maxritter/diy-thermocam/firmware/3.0/src/general/colorschemes.cpp

/*
 *
 * COLOR SCHEMES - Contains 19 different color schemes to display the thermal image
 *
 * DIY-Thermocam Firmware
 *
 * GNU General Public License v3.0
 *
 * Copyright by Max Ritter
 *
 * http://www.diy-thermocam.net
 * https://github.com/maxritter/diy-thermocam
 *
 */

/*################################# INCLUDES ##################################*/

#include <Arduino.h>
#include <colorschemes.h>

/*############################# PUBLIC VARIABLES ##############################*/

const byte colorMap_arctic[] = { 15, 16, 146, 15, 16, 146, 15, 15, 153, 15, 15, 153, 15, 15, 159, 15, 15, 159, 16, 15, 167, 16, 15, 167, 15, 15, 175, 15, 15, 175, 16, 15, 182, 16, 15, 182, 16, 16, 190, 16, 16, 190, 14, 15, 197, 14, 15, 197, 15, 15, 205, 15, 15, 205, 15, 15, 211, 15, 15, 211, 16, 15, 219, 16, 15, 219, 16, 15, 227, 16, 15, 227, 16, 18, 239, 16, 18, 239, 16, 25, 240, 16, 25, 240, 15, 34, 239, 15, 34, 239, 15, 44, 238, 15, 44, 238, 14, 54, 239, 14, 54, 239, 14, 63, 239, 14, 63, 239, 14, 74, 238, 14, 74, 238, 17, 82, 238, 17, 82, 238, 19, 92, 237, 19, 92, 237, 22, 102, 239, 22, 102, 239, 24, 111, 238, 24, 111, 238, 27, 120, 237, 27, 120, 237, 28, 131, 237, 28, 131, 237, 32, 140, 237, 32, 140, 237, 34, 150, 237, 34, 150, 237, 36, 160, 236, 36, 160, 236, 39, 168, 237, 39, 168, 237, 42, 179, 237, 42, 179, 237, 44, 188, 236, 44, 188, 236, 46, 197, 236, 46, 197, 236, 49, 208, 236, 49, 208, 236, 52, 217, 235, 52, 217, 235, 54, 227, 232, 54, 227, 232, 57, 227, 230, 57, 227, 230, 58, 226, 227, 58, 226, 227, 62, 224, 225, 62, 224, 225, 64, 222, 222, 64, 222, 222, 66, 220, 220, 66, 220, 220, 67, 215, 215, 67, 215, 215, 69, 209, 210, 69, 209, 210, 73, 205, 204, 73, 205, 204, 76, 198, 199, 76, 198, 199, 79, 193, 192, 79, 193, 192, 81, 187, 187, 81, 187, 187, 83, 181, 180, 83, 181, 180, 87, 175, 175, 87, 175, 175, 88, 170, 170, 88, 170, 170, 88, 164, 165, 88, 164, 165, 90, 158, 159, 90, 158, 159, 90, 152, 153, 90, 152, 153, 90, 146, 145, 90, 146, 145, 92, 140, 140, 92, 140, 140, 92, 134, 134, 92, 134, 134, 95, 129, 129, 95, 129, 129, 95, 123, 123, 95, 123, 123, 96, 117, 116, 96, 117, 116, 97, 111, 110, 97, 111, 110, 99, 105, 105, 99, 105, 105, 102, 102, 102, 102, 102, 102, 107, 101, 97, 107, 101, 97, 112, 101, 95, 112, 101, 95, 117, 101, 90, 117, 101, 90, 123, 102, 87, 123, 102, 87, 129, 101, 84, 129, 101, 84, 134, 101, 80, 134, 101, 80, 138, 102, 76, 138, 102, 76, 143, 101, 73, 143, 101, 73, 148, 101, 69, 148, 101, 69, 153, 101, 66, 153, 101, 66, 159, 102, 63, 159, 102, 63, 165, 102, 59, 165, 102, 59, 170, 101, 56, 170, 101, 56, 175, 101, 52, 175, 101, 52, 180, 101, 48, 180, 101, 48, 185, 100, 45, 185, 100, 45, 191, 100, 41, 191, 100, 41, 197, 101, 37, 197, 101, 37, 201, 101, 35, 201, 101, 35, 206, 101, 31, 206, 101, 31, 211, 101, 26, 211, 101, 26, 216, 101, 24, 216, 101, 24, 221, 101, 19, 221, 101, 19, 228, 101, 18, 228, 101, 18, 233, 101, 14, 233, 101, 14, 237, 101, 13, 237, 101, 13, 236, 105, 13, 236, 105, 13, 236, 112, 12, 236, 112, 12, 236, 120, 13, 236, 120, 13, 237, 123, 13, 237, 123, 13, 237, 130, 12, 237, 130, 12, 237, 137, 13, 237, 137, 13, 237, 142, 12, 237, 142, 12, 237, 149, 12, 237, 149, 12, 236, 156, 13, 236, 156, 13, 236, 160, 11, 236, 160, 11, 235, 167, 12, 235, 167, 12, 235, 173, 12, 235, 173, 12, 235, 179, 12, 235, 179, 12, 235, 185, 12, 235, 185, 12, 236, 191, 13, 236, 191, 13, 236, 196, 11, 236, 196, 11, 235, 202, 12, 235, 202, 12, 236, 204, 27, 236, 204, 27, 235, 207, 34, 235, 207, 34, 236, 208, 50, 236, 208, 50, 235, 211, 65, 235, 211, 65, 235, 212, 71, 235, 212, 71, 235, 214, 87, 235, 214, 87, 235, 216, 100, 235, 216, 100, 235, 216, 108, 235, 216, 108, 236, 220, 123, 236, 220, 123, 235, 221, 138, 235, 221, 138, 235, 221, 146, 235, 221, 146, 235, 225, 160, 235, 225, 160, 235, 225, 175, 235, 225, 175, 236, 227, 182, 236, 227, 182, 235, 229, 191, 235, 229, 191, 235, 230, 194, 235, 230, 194 };

const byte colorMap_blackHot[] = { 235, 235, 235, 234, 234, 234, 233, 233, 233, 232, 232, 232, 231, 231, 231, 230, 230, 230, 229, 229, 229, 228, 228, 228, 227, 227, 227, 226, 226, 226, 225, 225, 225, 224, 224, 224, 223, 223, 223, 222, 222, 222, 221, 221, 221, 220, 220, 220, 219, 219, 219, 218, 218, 218, 217, 217, 217, 216, 216, 216, 215, 215, 215, 214, 214, 214, 213, 213, 213, 212, 212, 212, 211, 211, 211, 210, 210, 210, 209, 209, 209, 209, 209, 209, 208, 208, 208, 207, 207, 207, 206, 206, 206, 205, 205, 205, 204, 204, 204, 203, 203, 203, 202, 202, 202, 201, 201, 201, 200, 200, 200, 199, 199, 199, 198, 198, 198, 197, 197, 197, 196, 196, 196, 195, 195, 195, 194, 194, 194, 193, 193, 193, 192, 192, 192, 191, 191, 191, 190, 190, 190, 189, 189, 189, 188, 188, 188, 187, 187, 187, 186, 186, 186, 185, 185, 185, 184, 184, 184, 183, 183, 183, 182, 182, 182, 181, 181, 181, 180, 180, 180, 179, 179, 179, 178, 178, 178, 177, 177, 177, 176, 176, 176, 175, 175, 175, 174, 174, 174, 173, 173, 173, 172, 172, 172, 171, 171, 171, 170, 170, 170, 169, 169, 169, 168, 168, 168, 167, 167, 167, 166, 166, 166, 165, 165, 165, 164, 164, 164, 163, 163, 163, 162, 162, 162, 161, 161, 161, 160, 160, 160, 159, 159, 159, 158, 158, 158, 157, 157, 157, 156, 156, 156, 155, 155, 155, 154, 154, 154, 154, 154, 154, 153, 153, 153, 152, 152, 152, 151, 151, 151, 150, 150, 150, 149, 149, 149, 148, 148, 148, 147, 147, 147, 146, 146, 146, 145, 145, 145, 144, 144, 144, 143, 143, 143, 142, 142, 142, 141, 141, 141, 140, 140, 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
225, 225, 225, 226, 226, 226, 227, 227, 227, 228, 228, 228, 229, 229, 229, 230, 230, 230, 231, 231, 231, 232, 232, 232, 233, 233, 233, 234, 234, 234, 235, 235, 235 };

const byte colorMap_contrast[] = { 16, 16, 16, 23, 16, 22, 30, 15, 30, 37, 16, 37, 46, 15, 45, 53, 15, 52, 60, 15, 60, 67, 15, 67, 75, 15, 75, 82, 15, 81, 89, 15, 90, 98, 14, 96, 105, 14, 105, 112, 14, 111, 120, 15, 121, 127, 15, 127, 135, 15, 135, 143, 14, 142, 150, 14, 150, 158, 14, 157, 165, 14, 165, 172, 14, 172, 179, 14, 180, 186, 14, 187, 195, 14, 195, 202, 14, 201, 209, 14, 210, 217, 14, 216, 209, 15, 214, 202, 14, 211, 194, 15, 209, 187, 14, 206, 179, 15, 204, 172, 14, 201, 165, 15, 199, 157, 14, 196, 150, 15, 194, 141, 14, 191, 135, 15, 189, 126, 14, 186, 120, 15, 184, 112, 14, 181, 105, 15, 179, 97, 14, 176, 91, 15, 174, 82, 14, 171, 74, 15, 169, 67, 14, 166, 60, 15, 164, 52, 14, 161, 45, 15, 159, 38, 14, 156, 30, 15, 154, 23, 14, 151, 15, 15, 149, 16, 23, 152, 14, 30, 155, 15, 38, 156, 15, 44, 158, 14, 53, 162, 14, 59, 164, 15, 67, 165, 13, 74, 168, 14, 82, 171, 15, 89, 174, 13, 96, 176, 14, 104, 178, 14, 111, 180, 13, 119, 183, 13, 125, 185, 14, 133, 187, 12, 140, 189, 13, 148, 192, 14, 155, 195, 12, 162, 198, 13, 170, 199, 13, 177, 201, 12, 185, 205, 12, 191, 207, 13, 199, 208, 11, 206, 211, 12, 214, 214, 12, 208, 206, 12, 205, 200, 12, 199, 192, 12, 194, 185, 12, 190, 176, 12, 185, 169, 14, 181, 162, 12, 176, 155, 13, 170, 147, 14, 166, 141, 13, 161, 133, 13, 156, 125, 14, 151, 119, 13, 147, 110, 14, 142, 103, 14, 137, 96, 13, 132, 88, 14, 128, 81, 14, 122, 74, 13, 118, 66, 14, 113, 60, 15, 108, 52, 14, 104, 44, 15, 99, 36, 15, 93, 29, 15, 90, 22, 15, 84, 15, 23, 89, 14, 28, 93, 13, 36, 97, 15, 42, 103, 14, 49, 106, 13, 55, 112, 13, 63, 116, 12, 69, 120, 13, 76, 125, 12, 84, 129, 12, 90, 134, 11, 97, 138, 10, 104, 143, 12, 111, 147, 11, 117, 152, 10, 124, 156, 9, 130, 161, 10, 138, 165, 10, 144, 170, 9, 151, 174, 9, 159, 179, 8, 165, 183, 9, 172, 187, 8, 179, 193, 8, 186, 196, 7, 192, 202, 6, 200, 206, 8, 205, 210, 7, 213, 215, 6, 209, 208, 7, 207, 201, 7, 204, 194, 7, 200, 187, 7, 196, 180, 8, 194, 173, 8, 191, 166, 8, 187, 159, 9, 183, 153, 9, 181, 145, 9, 178, 139, 10, 174, 132, 10, 172, 124, 10, 168, 118, 11, 166, 112, 10, 162, 105, 10, 160, 98, 11, 156, 91, 11, 153, 84, 11, 150, 77, 12, 147, 70, 12, 143, 63, 12, 140, 57, 13, 137, 49, 13, 134, 43, 13, 130, 36, 14, 127, 29, 14, 124, 22, 14, 121, 15, 15, 124, 16, 17, 128, 17, 19, 130, 20, 19, 133, 21, 21, 135, 21, 22, 139, 23, 24, 141, 25, 24, 144, 26, 26, 148, 28, 28, 151, 29, 30, 153, 31, 30, 156, 32, 32, 160, 34, 34, 163, 35, 36, 164, 36, 36, 168, 38, 38, 171, 39, 40, 174, 40, 42, 176, 43, 42, 180, 44, 44, 183, 45, 46, 187, 46, 48, 189, 49, 48, 191, 49, 49, 194, 50, 51, 198, 52, 53, 200, 54, 53, 203, 55, 55, 204, 60, 61, 205, 67, 68, 206, 73, 72, 207, 79, 79, 208, 84, 84, 209, 91, 91, 210, 96, 97, 211, 103, 104, 212, 109, 108, 213, 115, 114, 214, 120, 120, 215, 127, 127, 216, 132, 133, 217, 139, 139, 218, 145, 143, 219, 151, 150, 220, 156, 156, 221, 163, 163, 222, 168, 169, 223, 175, 175, 224, 181, 179, 225, 187, 186, 226, 192, 192, 227, 199, 199, 228, 204, 204, 229, 211, 211, 230, 217, 215, 231, 223, 222, 232, 228, 228 };

const byte colorMap_doubleRainbow[] = { 18, 15, 18, 25, 17, 26, 34, 18, 32, 43, 19, 39, 52, 21, 48, 60, 23, 55, 69, 25, 62, 77, 26, 70, 86, 28, 75, 95, 30, 84, 103, 31, 91, 112, 34, 98, 120, 35, 106, 129, 36, 111, 138, 39, 120, 146, 40, 128, 155, 42, 136, 150, 44, 140, 145, 47, 146, 139, 51, 151, 134, 54, 157, 130, 57, 161, 124, 60, 168, 119, 63, 172, 115, 66, 179, 109, 70, 183, 104, 73, 189, 99, 76, 194, 93, 80, 200, 89, 83, 205, 84, 86, 211, 78, 90, 216, 73, 92, 222, 69, 96, 227, 63, 99, 233, 59, 103, 238, 57, 104, 230, 54, 107, 221, 50, 109, 213, 50, 113, 206, 46, 115, 196, 45, 117, 189, 42, 120, 180, 39, 123, 171, 38, 125, 164, 35, 127, 154, 32, 130, 147, 30, 133, 138, 28, 135, 129, 25, 138, 122, 24, 140, 113, 21, 144, 104, 20, 146, 97, 16, 148, 87, 14, 152, 81, 27, 153, 75, 41, 157, 70, 54, 160, 64, 69, 164, 60, 84, 166, 54, 98, 170, 49, 110, 173, 44, 123, 176, 38, 138, 180, 34, 151, 182, 28, 166, 186, 23, 179, 189, 18, 194, 193, 13, 194, 189, 13, 194, 186, 13, 193, 183, 14, 194, 180, 15, 194, 177, 15, 194, 174, 14, 193, 171, 14, 194, 169, 15, 193, 165, 15, 194, 161, 16, 194, 160, 15, 194, 156, 17, 194, 154, 18, 195, 150, 17, 194, 147, 17, 195, 145, 18, 195, 142, 18, 195, 138, 19, 194, 135, 19, 195, 133, 20, 195, 129, 20, 195, 126, 19, 195, 124, 22, 193, 118, 21, 191, 114, 24, 189, 109, 24, 188, 104, 27, 186, 100, 27, 185, 95, 29, 183, 91, 30, 181, 86, 32, 180, 82, 33, 178, 77, 35, 177, 73, 36, 176, 67, 38, 173, 63, 39, 172, 59, 41, 172, 54, 41, 169, 50, 44, 169, 45, 45, 170, 53, 60, 171, 61, 74, 174, 68, 90, 174, 76, 103, 177, 83, 119, 179, 92, 133, 181, 99, 149, 182, 107, 162, 185, 114, 178, 186, 123, 192, 187, 131, 208, 190, 139, 222, 193, 146, 238, 194, 149, 236, 195, 153, 238, 197, 158, 237, 199, 160, 237, 200, 165, 237, 203, 168, 236, 193, 169, 235, 185, 168, 232, 176, 168, 229, 166, 168, 228, 157, 168, 225, 149, 168, 222, 140, 170, 220, 131, 169, 218, 121, 170, 215, 113, 170, 212, 103, 170, 211, 94, 170, 208, 86, 171, 206, 76, 171, 203, 68, 171, 202, 59, 171, 199, 51, 170, 196, 41, 171, 195, 33, 172, 193, 23, 172, 190, 14, 172, 187, 18, 173, 181, 24, 174, 174, 30, 175, 166, 33, 176, 160, 39, 177, 152, 45, 178, 145, 49, 179, 139, 54, 180, 131, 60, 181, 126, 64, 182, 118, 69, 183, 110, 74, 183, 104, 79, 185, 97, 84, 186, 91, 88, 187, 83, 93, 187, 76, 99, 189, 71, 103, 190, 63, 107, 191, 57, 113, 192, 50, 118, 193, 42, 122, 194, 36, 127, 195, 28, 133, 195, 20, 139, 196, 15, 143, 199, 14, 148, 200, 15, 151, 202, 13, 155, 204, 13, 161, 206, 15, 164, 208, 13, 169, 209, 13, 173, 211, 14, 178, 213, 13, 182, 214, 13, 187, 216, 14, 192, 217, 13, 196, 219, 13, 201, 221, 13, 205, 223, 13, 210, 224, 13, 213, 226, 11, 217, 228, 13, 222, 229, 13, 226, 231, 11, 231, 233, 13, 236, 234, 13, 236, 229, 13, 236, 224, 16, 237, 219, 17, 236, 214, 20, 236, 209, 22, 236, 203, 22, 236, 198, 25, 237, 193, 28, 236, 188, 30, 236, 183, 31, 236, 177, 33, 236, 172, 34, 236, 167, 36, 236, 162, 39, 238, 156, 42, 237, 151, 42, 237, 146, 45, 237, 140, 47, 238, 136, 48, 238, 131, 51, 237, 125, 53, 235, 118, 52, 235, 113, 52, 234, 105, 52, 233, 99, 52, 232, 93, 52, 231, 86, 53, 229, 80, 52, 230, 73, 52, 228, 67, 53, 227, 61, 53, 226, 54, 52, 225, 48, 52, 227, 56, 61, 227, 64, 69, 227, 73, 77, 227, 80, 86, 227, 88, 93, 229, 96, 101, 228, 105, 109, 230, 113, 118, 230, 121, 126, 231, 130, 136, 231, 138, 142, 230, 146, 150, 231, 154, 158, 233, 162, 166, 233, 170, 175, 232, 175, 178, 232, 179, 183, 233, 184, 189, 233, 189, 194, 233, 195, 198, 233, 199, 202, 235, 204, 206, 235, 208, 213, 234, 213, 216, 235, 218, 222, 235, 222, 227, 234, 227, 230, 235, 232, 235 };

const byte colorMap_grayRed[] = { 218, 186, 175, 216, 186, 174, 214, 186, 173, 213, 185, 172, 212, 184, 171, 209, 183, 170, 206, 182, 170, 205, 181, 169, 202, 180, 168, 202, 180, 168, 199, 179, 168, 197, 178, 167, 194, 178, 166, 193, 177, 166, 191, 177, 165, 186, 176, 165, 185, 175, 164, 182, 173, 162, 180, 174, 162, 177, 172, 162, 174, 172, 161, 172, 170, 159, 170, 170, 160, 168, 169, 159, 165, 169, 158, 162, 167, 157, 160, 168, 157, 157, 167, 155, 156, 166, 154, 153, 165, 155, 149, 164, 155, 146, 164, 154, 143, 163, 152, 140, 162, 153, 137, 161, 151, 136, 160, 150, 134, 159, 149, 131, 159, 150, 128, 157, 148, 126, 158, 148, 124, 156, 147, 122, 156, 146, 120, 155, 147, 117, 155, 146, 115, 154, 145, 110, 152, 144, 109, 152, 144, 106, 151, 142, 105, 150, 141, 101, 149, 141, 100, 149, 141, 99, 148, 140, 96, 148, 139, 93, 146, 138, 92, 147, 138, 91, 146, 137, 90, 145, 138, 86, 143, 136, 85, 142, 135, 83, 142, 134, 80, 142, 133, 77, 140, 133, 76, 139, 132, 75, 138, 131, 74, 137, 130, 72, 137, 129, 71, 136, 130, 69, 137, 128, 68, 136, 127, 67, 134, 128, 66, 133, 127, 65, 134, 127, 64, 133, 126, 63, 132, 125, 62, 131, 124, 61, 130, 123, 60, 129, 122, 59, 128, 121, 59, 128, 121, 58, 127, 120, 58, 125, 119, 58, 125, 119, 57, 124, 118, 58, 123, 117, 58, 123, 117, 58, 123, 117, 57, 122, 116, 56, 121, 115, 56, 121, 115, 57, 120, 115, 58, 117, 111, 58, 117, 111, 59, 116, 111, 59, 116, 111, 60, 114, 110, 60, 115, 108, 61, 114, 108, 61, 112, 107, 61, 112, 107, 63, 112, 107, 63, 112, 107, 63, 110, 104, 65, 109, 104, 66, 109, 104, 67, 108, 104, 69, 106, 102, 72, 107, 101, 72, 105, 100, 73, 104, 100, 75, 103, 100, 78, 102, 98, 77, 101, 97, 79, 102, 98, 82, 101, 96, 83, 100, 96, 85, 99, 96, 86, 99, 95, 89, 98, 93, 90, 97, 93, 92, 95, 92, 96, 94, 91, 97, 94, 91, 100, 93, 89, 103, 93, 90, 104, 93, 88, 107, 91, 88, 107, 90, 86, 111, 89, 87, 112, 89, 87, 114, 88, 85, 117, 87, 83, 120, 87, 84, 122, 86, 84, 125, 85, 82, 126, 84, 82, 130, 82, 81, 134, 82, 80, 135, 82, 78, 138, 81, 78, 140, 80, 78, 143, 80, 77, 145, 79, 77, 148, 78, 75, 150, 77, 75, 153, 77, 75, 154, 77, 73, 157, 75, 73, 159, 73, 72, 163, 73, 71, 164, 72, 71, 168, 70, 69, 171, 71, 69, 173, 70, 69, 176, 68, 67, 178, 68, 67, 180, 67, 65, 182, 66, 65, 184, 66, 66, 187, 65, 64, 188, 64, 64, 191, 63, 63, 193, 63, 63, 194, 62, 61, 197, 61, 61, 198, 60, 61, 202, 59, 57, 204, 58, 57, 205, 57, 57, 208, 58, 56, 209, 57, 56, 212, 56, 56, 213, 55, 55, 214, 54, 54, 216, 53, 52, 218, 52, 52, 219, 51, 52, 221, 51, 50, 222, 50, 50, 223, 49, 50, 225, 49, 48, 227, 47, 47, 228, 48, 48, 228, 46, 47, 229, 45, 46, 231, 45, 46, 231, 45, 46, 232, 44, 46, 233, 43, 43, 234, 42, 43, 234, 40, 42, 234, 40, 42, 236, 40, 42, 236, 38, 41, 236, 38, 39, 238, 37, 39, 236, 35, 37, 237, 35, 35, 237, 35, 35, 236, 34, 36, 238, 33, 34, 237, 32, 35, 238, 31, 35, 237, 31, 32, 236, 30, 31, 235, 29, 30, 235, 29, 30, 235, 29, 30, 234, 28, 29, 234, 26, 28, 233, 25, 27, 232, 24, 26, 232, 24, 26, 231, 23, 25, 231, 23, 25, 230, 22, 24, 232, 21, 24, 231, 20, 23, 230, 19, 22, 229, 18, 21, 230, 18, 21, 229, 17, 20, 229, 17, 20, 228, 16, 19, 227, 15, 18 };

const byte colorMap_glowBow[] = { 16, 16, 16, 19, 17, 18, 22, 16, 16, 25, 17, 18, 28, 17, 19, 31, 17, 20, 34, 17, 19, 36, 18, 20, 39, 18, 19, 43, 19, 21, 45, 18, 21, 48, 20, 21, 52, 19, 22, 54, 20, 23, 58, 20, 23, 63, 21, 23, 68, 21, 25, 70, 21, 26, 73, 22, 27, 75, 22, 26, 79, 22, 27, 81, 22, 28, 84, 23, 27, 87, 22, 28, 91, 24, 30, 96, 23, 30, 102, 24, 33, 104, 25, 32, 108, 25, 33, 110, 25, 34, 117, 25, 34, 120, 27, 34, 122, 27, 35, 127, 28, 35, 129, 27, 35, 132, 29, 37, 135, 27, 37, 138, 29, 38, 141, 29, 39, 143, 29, 40, 147, 29, 41, 150, 31, 41, 152, 30, 41, 155, 29, 42, 158, 30, 41, 165, 31, 44, 167, 32, 43, 170, 32, 44, 175, 33, 45, 177, 33, 46, 178, 32, 46, 182, 32, 45, 186, 33, 47, 188, 34, 48, 190, 34, 47, 194, 34, 48, 195, 35, 49, 195, 35, 47, 197, 38, 48, 196, 39, 46, 198, 39, 45, 199, 41, 44, 200, 42, 43, 201, 43, 43, 200, 44, 41, 201, 45, 42, 203, 46, 41, 204, 47, 42, 204, 47, 40, 205, 49, 40, 205, 49, 38, 206, 52, 38, 207, 52, 36, 208, 53, 37, 209, 54, 36, 210, 55, 36, 210, 58, 35, 211, 59, 34, 212, 60, 33, 213, 60, 33, 214, 61, 33, 213, 62, 31, 215, 64, 33, 215, 64, 31, 216, 66, 30, 218, 66, 30, 218, 66, 30, 218, 68, 29, 219, 70, 28, 220, 69, 28, 221, 72, 26, 223, 73, 26, 222, 74, 24, 223, 75, 25, 224, 76, 24, 225, 78, 23, 225, 78, 22, 226, 79, 23, 227, 80, 22, 227, 81, 20, 228, 82, 21, 229, 83, 20, 230, 83, 18, 231, 86, 19, 231, 86, 17, 232, 87, 16, 233, 88, 17, 234, 90, 16, 235, 91, 14, 235, 91, 14, 236, 93, 13, 237, 94, 12, 236, 96, 13, 237, 97, 13, 237, 99, 1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
		188, 188, 189, 189, 189, 190, 190, 190, 191, 191, 191, 192, 192, 192, 193, 193, 193, 194, 194, 194, 195, 195, 195, 196, 196, 196, 197, 197,
		197, 198, 198, 198, 199, 199, 199, 200, 200, 200, 201, 201, 201, 202, 202, 202, 203, 203, 203, 204, 204, 204, 205, 205, 205, 206, 206, 206,
		207, 207, 207, 208, 208, 208, 209, 209, 209, 210, 210, 210, 211, 211, 211, 212, 212, 212, 213, 213, 213, 214, 214, 214, 215, 215, 215, 216,
		216, 216, 217, 217, 217, 218, 218, 218, 219, 219, 219, 220, 220, 220, 221, 221, 221, 222, 222, 222, 223, 223, 223, 224, 224, 224, 225, 225,
		225, 226, 226, 226, 227, 227, 227, 228, 228, 228, 229, 229, 229, 230, 230, 230, 231, 231, 231, 232, 232, 232, 233, 233, 233, 234, 234, 234,
		235, 235, 235, 236, 236, 236, 237, 237, 237, 238, 238, 238, 239, 239, 239, 240, 240, 240, 241, 241, 241, 242, 242, 242, 243, 243, 243, 244,
		244, 244, 245, 245, 245, 246, 246, 246, 247, 247, 247, 248, 248, 248, 249, 249, 249, 250, 250, 250, 251, 251, 251, 252, 252, 252, 253, 253,
		253, 254, 254, 254, 255, 255, 255 };

const byte colorMap_hottest[] = { 16, 16, 16, 17, 17, 17, 18, 18, 18, 19, 19, 19, 20, 20, 20, 21, 21, 21, 22, 22, 22, 23, 23, 23, 24, 24, 24, 25, 25, 25, 26, 26, 26, 27, 27, 27, 28, 28, 28, 29, 29, 29, 30, 30, 30, 31, 31, 31, 32, 32, 32, 33, 33, 33, 34, 34, 34, 35, 35, 35, 36, 36, 36, 37, 37, 37, 38, 38, 38, 39, 39, 39, 40, 40, 40, 41, 41, 41, 42, 42, 42, 43, 43, 43, 44, 44, 44, 44, 44, 44, 45, 45, 45, 46, 46, 46, 47, 47, 47, 48, 48, 48, 49, 49, 49, 50, 50, 50, 51, 51, 51, 52, 52, 52, 53, 53, 53, 54, 54, 54, 55, 55, 55, 56, 56, 56, 57, 57, 57, 58, 58, 58, 59, 59, 59, 60, 60, 60, 61, 61, 61, 62, 62, 62, 63, 63, 63, 64, 64, 64, 65, 65, 65, 66, 66, 66, 67, 67, 67, 68, 68, 68, 69, 69, 69, 70, 70, 70, 71, 71, 71, 72, 72, 72, 73, 73, 73, 74, 74, 74, 75, 75, 75, 76, 76, 76, 77, 77, 77, 78, 78, 78, 79, 79, 79, 80, 80, 80, 81, 81, 81, 82, 82, 82, 83, 83, 83, 84, 84, 84, 85, 85, 85, 86, 86, 86, 87, 87, 87, 88, 88, 88, 89, 89, 89, 90, 90, 90, 91, 91, 91, 92, 92, 92, 93, 93, 93, 94, 94, 94, 95, 95, 95, 96, 96, 96, 97, 97, 97, 98, 98, 98, 99, 99, 99, 99, 99, 99, 100, 100, 100, 101, 101, 101, 102, 102, 102, 103, 103, 103, 104, 104, 104, 105, 105, 105, 106, 106, 106, 107, 107, 107, 108, 108, 108, 109, 109, 109, 110, 110, 110, 111, 111, 111, 112, 112, 112, 113, 113, 113, 114, 114, 114, 115, 115, 115, 116, 116, 116, 117, 117, 117, 118, 118, 118, 119, 119, 119, 120, 120, 120, 121, 121, 121, 122, 122, 122, 123, 123, 123, 124, 124, 124, 125, 125, 125, 126, 126, 126, 127, 127, 127, 128, 128, 128,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
		75, 218, 49, 69, 221, 52, 64, 223, 55, 59, 224, 57, 49, 225, 60, 47, 226, 64, 44, 227, 67, 42, 228, 71, 39, 229, 74, 37, 230, 78, 34, 231, 81,
		32, 231, 85, 29, 232, 88, 27, 233, 92, 24, 234, 95, 22, 235, 99, 19, 236, 102, 17, 237, 106, 14, 238, 109, 12, 239, 112, 12, 240, 116, 12,
		240, 119, 12, 241, 123, 12, 241, 127, 12, 242, 130, 12, 242, 134, 12, 243, 138, 12, 243, 141, 13, 244, 145, 13, 244, 149, 13, 245, 152, 13,
		245, 156, 13, 246, 160, 13, 246, 163, 13, 247, 167, 13, 247, 171, 13, 248, 175, 14, 248, 178, 15, 249, 182, 16, 249, 185, 18, 250, 189, 19,
		250, 192, 20, 251, 196, 21, 251, 199, 22, 252, 203, 23, 252, 206, 24, 253, 210, 25, 253, 213, 27, 254, 217, 28, 254, 220, 29, 255, 224, 30,
		255, 227, 39, 255, 229, 53, 255, 231, 67, 255, 233, 81, 255, 234, 95, 255, 236, 109, 255, 238, 123, 255, 240, 137, 255, 242, 151, 255, 244,
		165, 255, 246, 179, 255, 248, 193, 255, 249, 207, 255, 251, 221, 255, 253, 235, 255, 255, 24 };

const byte colorMap_lava[] = { 16, 16, 16, 17, 19, 22, 19, 21, 30, 20, 24, 37, 22, 27, 43, 22, 31, 50, 24, 32, 57, 25, 37, 65, 26, 39, 70, 28, 43, 78, 29, 44, 85, 31, 47, 94, 32, 50, 100, 34, 53, 107, 34, 57, 113, 37, 59, 122, 37, 63, 128, 39, 66, 135, 40, 69, 141, 42, 71, 149, 44, 74, 156, 41, 76, 156, 41, 76, 156, 39, 78, 157, 36, 80, 155, 36, 82, 156, 34, 82, 156, 33, 85, 157, 31, 86, 157, 30, 86, 157, 29, 88, 156, 28, 91, 157, 26, 91, 157, 26, 93, 158, 23, 95, 158, 21, 97, 159, 20, 98, 159, 18, 99, 158, 17, 101, 160, 15, 102, 159, 15, 104, 160, 13, 105, 158, 13, 105, 158, 14, 106, 157, 13, 107, 157, 14, 108, 156, 14, 110, 156, 14, 111, 154, 15, 112, 155, 13, 113, 153, 13, 113, 151, 14, 114, 152, 14, 114, 151, 14, 116, 152, 14, 116, 150, 13, 118, 149, 13, 119, 147, 14, 120, 148, 13, 121, 146, 14, 122, 146, 14, 122, 146, 14, 124, 145, 14, 125, 143, 15, 126, 144, 14, 125, 143, 15, 126, 142, 13, 127, 142, 14, 128, 142, 14, 128, 140, 14, 130, 139, 14, 130, 139, 14, 130, 139, 14, 131, 137, 13, 133, 136, 13, 133, 135, 14, 134, 136, 13, 135, 134, 13, 135, 134, 13, 135, 134, 14, 137, 133, 14, 137, 131, 19, 133, 130, 24, 130, 132, 30, 125, 131, 35, 121, 130, 39, 118, 129, 46, 114, 129, 50, 109, 127, 56, 106, 127, 62, 101, 128, 67, 99, 126, 73, 94, 125, 78, 90, 126, 84, 85, 125, 89, 82, 124, 93, 78, 123, 99, 73, 122, 105, 70, 122, 109, 66, 121, 115, 62, 122, 120, 58, 121, 123, 57, 119, 124, 57, 115, 127, 56, 114, 130, 54, 112, 133, 54, 108, 134, 53, 108, 136, 51, 104, 137, 51, 102, 140, 50, 100, 144, 50, 98, 145, 50, 96, 148, 49, 94, 148, 47, 91, 151, 46, 90, 154, 45, 88, 155, 45, 84, 158, 44, 84, 161, 43, 81, 162, 42, 79, 165, 41, 77, 167, 41, 75, 168, 41, 74, 169, 40, 72, 171, 40, 72, 172, 39, 70, 174, 39, 67, 175, 38, 67, 176, 38, 65, 178, 38, 63, 180, 38, 62, 182, 38, 60, 183, 37, 60, 184, 37, 59, 186, 37, 57, 187, 36, 55, 189, 36, 53, 190, 35, 53, 191, 35, 52, 193, 34, 50, 194, 34, 48, 196, 36, 48, 199, 37, 48, 201, 39, 48, 203, 40, 47, 205, 41, 46, 207, 43, 48, 210, 43, 47, 212, 46, 48, 213, 47, 47, 215, 47, 46, 219, 49, 46, 220, 50, 46, 222, 53, 46, 224, 53, 47, 227, 55, 47, 228, 56, 46, 229, 57, 45, 233, 59, 46, 235, 60, 45, 237, 62, 45, 238, 63, 44, 237, 65, 41, 236, 67, 40, 237, 68, 39, 236, 70, 36, 237, 71, 35, 237, 73, 34, 238, 74, 33, 237, 77, 31, 237, 79, 30, 237, 79, 27, 237, 83, 25, 236, 84, 23, 237, 86, 21, 237, 88, 20, 237, 88, 16, 236, 90, 16, 237, 92, 15, 237, 94, 12, 237, 97, 13, 237, 99, 12, 236, 103, 12, 237, 106, 12, 236, 110, 12, 237, 113, 13, 237, 116, 13, 236, 120, 13, 237, 123, 13, 236, 127, 14, 237, 130, 14, 236, 132, 13, 236, 135, 13, 236, 139, 12, 235, 143, 12, 236, 146, 12, 237, 149, 12, 236, 153, 13, 235, 155, 12, 236, 158, 12, 237, 161, 12, 236, 163, 12, 236, 165, 13, 235, 167, 12, 236, 170, 12, 236, 172, 11, 235, 173, 12, 236, 176, 12, 235, 179, 12, 235, 181, 11, 236, 183, 13, 235, 185, 12, 235, 187, 11, 236, 189, 11, 236, 191, 13, 235, 194, 12, 236, 196, 11, 236, 199, 11, 236, 200, 12, 235, 202, 12, 236, 205, 23, 235, 207, 34, 235, 208, 45, 236, 209, 56, 235, 211, 67, 234, 212, 78, 236, 214, 90, 235, 216, 100, 234, 218, 111, 236, 220, 123, 234, 220, 133, 235, 221, 146, 235, 224, 157, 236, 225, 167, 235, 226, 179, 235, 229, 191, 235, 229, 201, 235, 232, 213, 235, 233, 224, 235, 235, 235 };

const byte colorMap_medical[] = { 36, 36, 198, 36, 36, 198, 36, 36, 198, 36, 36, 198, 36, 36, 198, 36, 36, 198, 36, 36, 198, 36, 36, 198, 36, 36, 198, 36, 36, 198, 36, 36, 198, 36, 36, 198, 36, 36, 198, 36, 36, 198, 36, 36, 198, 36, 36, 198, 36, 36, 198, 36, 36, 198, 36, 36, 198, 36, 36, 198, 36, 36, 198, 36, 36, 198, 70, 71, 238, 70, 71, 238, 70, 71, 238, 70, 71, 238, 70, 71, 238, 70, 71, 238, 70, 71, 238, 70, 71, 238, 70, 71, 238, 70, 71, 238, 70, 71, 238, 70, 71, 238, 70, 71, 238, 70, 71, 238, 70, 71, 238, 70, 71, 238, 70, 71, 238, 70, 71, 238, 70, 71, 238, 70, 71, 238, 70, 71, 238, 70, 71, 238, 70, 71, 238, 25, 172, 193, 25, 172, 193, 25, 172, 193, 25, 172, 193, 25, 172, 193, 25, 172, 193, 25, 172, 193, 25, 172, 193, 25, 172, 193, 25, 172, 193, 25, 172, 193, 25, 172, 193, 25, 172, 193, 25, 172, 193, 25, 172, 193, 25, 172, 193, 25, 172, 193, 25, 172, 193, 25, 172, 193, 25, 172, 193, 25, 172, 193, 25, 172, 193, 14, 158, 13, 14, 158, 13, 14, 158, 13, 14, 158, 13, 14, 158, 13, 14, 158, 13, 14, 158, 13, 14, 158, 13, 14, 158, 13, 14, 158, 13, 14, 158, 13, 14, 158, 13, 14, 158, 13, 14, 158, 13, 14, 158, 13, 14, 158, 13, 14, 158, 13, 14, 158, 13, 14, 158, 13, 14, 158, 13, 14, 158, 13, 14, 158, 13, 14, 158, 13, 15, 15, 123, 15, 15, 123, 15, 15, 123, 15, 15, 123, 15, 15, 123, 15, 15, 123, 15, 15, 123, 15, 15, 123, 15, 15, 123, 15, 15, 123, 15, 15, 123, 15, 15, 123, 15, 15, 123, 15, 15, 123, 15, 15, 123, 15, 15, 123, 15, 15, 123, 15, 15, 123, 15, 15, 123, 15, 15, 123, 15, 15, 123, 1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
		251, 29, 61, 251, 28, 62, 250, 27, 63, 250, 27, 65, 249, 26, 66, 249, 26, 68, 248, 25, 70, 248, 24, 73, 247, 24, 75, 247, 25, 77, 247, 25, 79,
		247, 26, 81, 247, 32, 83, 247, 35, 85, 247, 38, 86, 247, 42, 88, 247, 46, 90, 247, 50, 92, 248, 55, 94, 248, 59, 96, 248, 64, 98, 248, 72,
		101, 249, 81, 104, 249, 87, 106, 250, 93, 108, 250, 95, 109, 250, 98, 110, 250, 100, 111, 251, 101, 112, 251, 102, 113, 251, 109, 117, 252,
		116, 121, 252, 121, 123, 253, 126, 126, 253, 130, 128, 254, 135, 131, 254, 139, 133, 254, 144, 136, 254, 151, 140, 255, 158, 144, 255, 163,
		146, 255, 168, 149, 255, 173, 152, 255, 176, 153, 255, 178, 155, 255, 184, 160, 255, 191, 165, 255, 195, 168, 255, 199, 172, 255, 203, 175,
		255, 207, 179, 255, 211, 182, 255, 216, 185, 255, 218, 190, 255, 220, 196, 255, 222, 200, 255, 225, 202, 255, 227, 204, 255, 230, 206, 255,
		233, 208 };

const byte colorMap_wheel1[] = { 238, 14, 239, 234, 17, 234, 229, 22, 230, 225, 27, 225, 221, 30, 220, 216, 35, 216, 211, 39, 212, 208, 44, 207, 203, 48, 202, 198, 52, 199, 195, 56, 195, 190, 61, 191, 185, 65, 185, 180, 70, 181, 177, 74, 177, 172, 79, 172, 167, 83, 167, 163, 87, 163, 159, 92, 158, 154, 97, 154, 150, 100, 151, 145, 105, 146, 141, 109, 142, 138, 114, 138, 132, 117, 132, 127, 122, 128, 124, 127, 124, 119, 131, 119, 114, 135, 114, 111, 140, 110, 106, 144, 105, 101, 149, 101, 97, 152, 98, 93, 157, 93, 88, 162, 89, 85, 166, 85, 79, 170, 79, 75, 175, 75, 71, 179, 71, 67, 184, 66, 61, 188, 61, 57, 193, 57, 53, 197, 52, 49, 201, 50, 43, 205, 45, 40, 209, 40, 35, 214, 36, 31, 219, 32, 27, 222, 26, 22, 227, 22, 17, 232, 18, 14, 236, 13, 14, 232, 18, 14, 227, 24, 14, 224, 27, 14, 218, 31, 13, 214, 36, 14, 209, 39, 13, 205, 44, 14, 200, 50, 13, 197, 53, 14, 192, 58, 14, 188, 61, 13, 184, 66, 14, 179, 71, 13, 176, 75, 14, 171, 80, 13, 167, 85, 14, 162, 88, 14, 158, 93, 14, 153, 98, 14, 150, 102, 15, 145, 107, 14, 141, 112, 15, 136, 115, 14, 132, 120, 15, 127, 125, 14, 124, 129, 15, 119, 134, 15, 115, 139, 15, 110, 142, 15, 106, 147, 16, 102, 151, 15, 98, 156, 16, 93, 161, 15, 89, 164, 16, 84, 169, 14, 79, 173, 15, 75, 177, 15, 71, 182, 15, 66, 187, 15, 62, 190, 14, 58, 195, 15, 53, 200, 14, 49, 204, 15, 45, 209, 15, 40, 214, 15, 36, 217, 15, 32, 222, 16, 27, 227, 15, 23, 231, 16, 19, 236, 15, 14, 241, 20, 18, 235, 25, 23, 232, 28, 28, 226, 32, 32, 222, 38, 36, 219, 42, 40, 213, 45, 45, 209, 51, 50, 204, 55, 53, 200, 58, 58, 196, 62, 62, 190, 68, 66, 187, 72, 70, 181, 75, 75, 177, 81, 79, 174, 85, 83, 168, 88, 88, 164, 93, 93, 159, 98, 96, 155, 102, 100, 151, 106, 106, 146, 111, 109, 142, 115, 113, 136, 119, 119, 133, 124, 122, 129, 128, 126, 123, 133, 131, 120, 136, 136, 116, 141, 140, 110, 145, 143, 106, 149, 149, 101, 154, 153, 97, 158, 156, 93, 163, 161, 88, 166, 166, 84, 171, 170, 78, 176, 174, 75, 179, 179, 71, 184, 183, 65, 189, 187, 62, 193, 191, 56, 196, 196, 52, 202, 200, 49, 206, 204, 43, 209, 209, 39, 215, 214, 34, 219, 217, 30, 223, 221, 26, 226, 226, 20, 232, 230, 17, 236, 234, 13, 231, 235, 15, 228, 235, 21, 223, 235, 25, 219, 234, 29, 214, 235, 34, 209, 235, 38, 206, 235, 43, 201, 235, 48, 197, 235, 52, 192, 235, 56, 188, 234, 61, 184, 235, 66, 180, 235, 70, 175, 235, 74, 169, 235, 79, 166, 235, 81, 161, 236, 87, 158, 235, 91, 152, 235, 95, 149, 235, 100, 143, 235, 104, 141, 235, 109, 135, 235, 114, 130, 235, 118, 126, 235, 122, 121, 235, 126, 118, 235, 132, 113, 235, 136, 109, 235, 140, 104, 235, 145, 100, 234, 149, 96, 236, 153, 91, 236, 157, 87, 235, 161, 82, 235, 166, 78, 235, 170, 74, 236, 175, 70, 235, 180, 65, 235, 184, 61, 235, 188, 57, 236, 193, 52, 236, 198, 48, 235, 202, 43, 235, 206, 39, 235, 211, 35, 236, 216, 31, 235, 220, 26, 236, 223, 22, 235, 227, 17, 235, 232, 14, 236, 237, 17, 231, 233, 21, 227, 228, 26, 222, 224, 31, 219, 219, 34, 214, 215, 39, 209, 210, 43, 205, 206, 49, 201, 202, 53, 196, 198, 56, 192, 192, 62, 188, 189, 66, 183, 186, 71, 179, 180, 74, 174, 176, 79, 171, 172, 84, 166, 168, 88, 161, 163, 94, 157, 160, 97, 153, 154, 101, 149, 150, 106, 144, 145, 110, 140, 142, 115, 135, 137, 119, 131, 133, 123, 127, 127, 129, 122, 125, 132, 118, 119, 136, 114, 115, 142, 110, 111, 146, 105, 107, 151, 100, 101, 154, 96, 98, 159, 93, 93, 164, 87, 89, 167, 83, 84, 172, 78, 80, 177, 75, 75, 181, 70, 72, 186, 66, 66, 190, 62, 63, 195, 57, 60, 199, 53, 54, 202, 48, 50, 208, 44, 46, 212, 40, 42, 217, 35, 36, 221, 30, 33, 225, 27, 28, 230, 22, 24, 234, 18, 19, 240, 14, 16 };

const byte colorMap_wheel2[] = { 17, 14, 17, 16, 23, 17, 17, 32, 17, 16, 40, 16, 16, 49, 16, 15, 58, 16, 15, 65, 16, 14, 74, 16, 15, 82, 16, 15, 91, 15, 14, 100, 15, 15, 108, 15, 14, 117, 14, 15, 125, 16, 14, 134, 15, 14, 143, 15, 15, 151, 15, 14, 160, 14, 15, 168, 14, 14, 177, 14, 14, 186, 13, 13, 192, 14, 13, 201, 14, 14, 209, 13, 14, 219, 14, 13, 228, 14, 14, 236, 13, 22, 227, 22, 28, 219, 29, 37, 212, 37, 46, 204, 46, 52, 196, 53, 61, 188, 61, 69, 181, 69, 76, 172, 76, 85, 164, 85, 94, 156, 95, 102, 147, 102, 109, 140, 110, 117, 132, 117, 126, 123, 126, 133, 116, 134, 141, 108, 141, 149, 101, 149, 157, 93, 157, 165, 84, 165, 174, 76, 175, 183, 68, 183, 189, 60, 190, 198, 52, 198, 205, 45, 205, 213, 36, 214, 222, 29, 222, 228, 21, 229, 238, 14, 239, 233, 17, 238, 229, 22, 238, 223, 27, 239, 218, 31, 238, 213, 37, 238, 209, 41, 238, 204, 45, 239, 199, 51, 239, 195, 55, 238, 191, 60, 238, 185, 65, 237, 180, 69, 238, 177, 74, 239, 171, 79, 238, 167, 84, 238, 161, 89, 239, 157, 93, 238, 153, 98, 239, 147, 101, 237, 142, 107, 237, 138, 111, 238, 133, 115, 237, 128, 121, 238, 123, 125, 237, 118, 131, 237, 114, 135, 238, 109, 139, 237, 104, 145, 237, 100, 149, 238, 96, 154, 239, 91, 159, 238, 85, 163, 237, 82, 169, 237, 76, 173, 238, 71, 177, 238, 67, 182, 237, 61, 187, 236, 57, 192, 236, 52, 196, 237, 47, 201, 237, 43, 206, 237, 37, 210, 238, 33, 215, 238, 29, 220, 237, 23, 226, 237, 19, 230, 237, 15, 235, 237, 19, 229, 232, 24, 226, 228, 28, 221, 224, 33, 216, 218, 36, 212, 214, 42, 208, 210, 46, 203, 206, 49, 199, 201, 54, 194, 197, 59, 191, 192, 64, 185, 188, 68, 181, 183, 73, 176, 179, 76, 172, 175, 81, 168, 171, 86, 163, 167, 91, 158, 162, 95, 155, 157, 100, 150, 153, 104, 146, 148, 108, 141, 144, 114, 137, 139, 117, 133, 136, 121, 129, 130, 126, 123, 126, 131, 118, 123, 136, 115, 118, 139, 111, 114, 144, 106, 109, 148, 101, 105, 154, 97, 100, 157, 93, 97, 161, 89, 91, 167, 85, 86, 172, 79, 83, 176, 75, 77, 179, 71, 73, 184, 66, 70, 189, 61, 64, 194, 57, 61, 197, 53, 56, 202, 48, 52, 207, 45, 47, 212, 39, 44, 216, 35, 38, 219, 31, 34, 225, 27, 30, 229, 22, 26, 234, 17, 20, 239, 14, 18, 233, 14, 22, 230, 13, 26, 224, 14, 31, 219, 14, 35, 214, 14, 39, 210, 13, 45, 206, 14, 49, 201, 14, 55, 195, 14, 59, 190, 14, 64, 186, 14, 68, 181, 14, 72, 176, 14, 77, 173, 14, 84, 168, 14, 88, 163, 14, 92, 158, 14, 97, 152, 14, 101, 147, 14, 107, 143, 14, 111, 139, 15, 117, 133, 14, 120, 130, 14, 125, 125, 14, 131, 120, 14, 136, 115, 14, 140, 109, 14, 144, 106, 14, 149, 100, 13, 155, 96, 15, 158, 91, 15, 164, 87, 14, 169, 82, 14, 173, 77, 14, 177, 72, 14, 182, 66, 14, 186, 64, 14, 193, 58, 15, 197, 53, 15, 202, 48, 15, 206, 44, 14, 210, 39, 14, 216, 34, 14, 221, 30, 13, 225, 24, 15, 230, 20, 15, 235, 15, 14, 241, 20, 18, 237, 23, 21, 232, 27, 26, 228, 30, 29, 223, 36, 33, 220, 38, 37, 215, 42, 41, 211, 45, 45, 207, 50, 49, 203, 54, 52, 199, 58, 56, 195, 61, 60, 192, 66, 64, 188, 69, 68, 184, 73, 72, 180, 78, 75, 176, 82, 79, 172, 84, 82, 167, 89, 87, 164, 91, 90, 159, 97, 95, 156, 100, 98, 151, 104, 103, 147, 108, 105, 144, 112, 109, 140, 115, 113, 136, 120, 117, 132, 124, 121, 128, 127, 125, 124, 131, 129, 120, 134, 133, 116, 139, 137, 111, 143, 140, 107, 148, 144, 105, 151, 148, 101, 155, 152, 97, 158, 156, 93, 162, 160, 89, 167, 164, 85, 169, 167, 80, 173, 171, 75, 176, 175, 71, 181, 179, 67, 185, 182, 63, 189, 186, 61, 192, 190, 57, 197, 194, 53, 200, 198, 49, 204, 202, 45, 209, 205, 40, 213, 209, 36, 216, 213, 32, 220, 217, 28, 223, 221, 24, 228, 225, 20, 232, 229, 16, 235, 233, 14 };

const byte colorMap_wheel3[] = { 17, 14, 17, 20, 14, 26, 26, 15, 36, 30, 14, 46, 35, 15, 56, 39, 15, 65, 45, 15, 75, 49, 14, 84, 55, 14, 94, 60, 15, 104, 64, 14, 113, 70, 14, 123, 74, 14, 132, 79, 15, 142, 83, 14, 152, 89, 15, 162, 93, 14, 171, 98, 15, 181, 103, 14, 190, 108, 14, 200, 112, 14, 209, 118, 14, 219, 122, 13, 228, 128, 13, 240, 122, 22, 228, 115, 33, 218, 111, 41, 211, 107, 50, 201, 102, 60, 190, 96, 70, 181, 91, 80, 170, 87, 89, 160, 81, 99, 151, 76, 109, 140, 70, 119, 130, 66, 130, 120, 63, 137, 113, 58, 148, 101, 54, 158, 93, 47, 167, 83, 44, 177, 72, 39, 187, 63, 35, 196, 54, 29, 206, 42, 24, 216, 33, 19, 225, 24, 15, 235, 12, 24, 225, 23, 34, 215, 34, 43, 206, 43, 52, 196, 51, 63, 187, 63, 72, 177, 71, 82, 166, 82, 93, 157, 92, 102, 148, 100, 111, 137, 111, 121, 129, 120, 131, 119, 131, 141, 110, 140, 150, 100, 151, 159, 90, 159, 169, 81, 171, 179, 71, 179, 188, 61, 188, 199, 51, 199, 209, 42, 208, 218, 31, 218, 228, 23, 228, 238, 14, 239, 227, 22, 235, 218, 33, 227, 208, 40, 225, 200, 51, 219, 189, 60, 214, 179, 71, 207, 170, 79, 204, 161, 89, 201, 150, 99, 192, 140, 109, 191, 130, 118, 186, 120, 128, 179, 111, 137, 174, 100, 147, 169, 91, 156, 164, 81, 166, 159, 71, 175, 152, 61, 185, 147, 53, 195, 143, 42, 205, 138, 32, 216, 134, 23, 225, 129, 13, 236, 125, 25, 225, 125, 34, 215, 126, 42, 206, 124, 52, 195, 125, 63, 187, 125, 72, 177, 125, 82, 166, 126, 92, 158, 126, 102, 148, 126, 112, 138, 125, 120, 128, 126, 131, 120, 125, 140, 109, 126, 150, 100, 125, 159, 90, 125, 170, 80, 127, 180, 71, 125, 189, 61, 126, 198, 53, 126, 208, 42, 126, 218, 33, 125, 227, 23, 126, 238, 14, 125, 228, 23, 130, 219, 32, 135, 208, 42, 140, 199, 52, 145, 189, 61, 150, 178, 71, 153, 169, 80, 158, 158, 90, 163, 149, 100, 169, 140, 109, 173, 130, 118, 178, 119, 128, 181, 110, 138, 189, 101, 147, 192, 90, 157, 196, 80, 166, 201, 71, 176, 207, 60, 186, 212, 51, 195, 217, 41, 205, 220, 31, 216, 225, 21, 224, 234, 15, 235, 237, 23, 225, 227, 33, 214, 217, 43, 204, 208, 53, 195, 197, 63, 184, 187, 72, 175, 178, 83, 166, 168, 91, 157, 159, 101, 146, 151, 111, 136, 142, 120, 127, 131, 130, 117, 122, 140, 109, 113, 150, 99, 102, 160, 89, 93, 168, 80, 83, 178, 70, 72, 189, 61, 64, 198, 52, 53, 210, 41, 46, 218, 31, 34, 229, 23, 24, 239, 14, 18, 229, 18, 25, 218, 23, 35, 208, 28, 45, 199, 32, 54, 189, 37, 64, 180, 41, 72, 170, 46, 82, 160, 50, 91, 151, 56, 102, 140, 60, 111, 132, 65, 120, 121, 69, 130, 110, 75, 143, 101, 79, 150, 92, 83, 160, 81, 89, 168, 73, 93, 178, 62, 98, 188, 52, 102, 200, 43, 109, 209, 33, 112, 217, 24, 118, 228, 15, 122, 238, 24, 123, 228, 34, 122, 218, 43, 123, 208, 53, 123, 199, 62, 123, 189, 71, 122, 179, 80, 123, 170, 91, 123, 160, 100, 122, 150, 109, 122, 140, 118, 123, 130, 131, 123, 122, 142, 123, 112, 151, 122, 102, 160, 123, 92, 170, 123, 83, 179, 124, 72, 189, 122, 63, 199, 123, 52, 208, 123, 44, 219, 123, 33, 227, 123, 24, 237, 122, 15, 228, 117, 24, 218, 113, 33, 209, 107, 44, 200, 102, 51, 190, 98, 61, 178, 93, 74, 169, 90, 81, 162, 84, 94, 151, 79, 104, 141, 74, 113, 132, 70, 123, 122, 65, 132, 112, 61, 142, 103, 55, 151, 93, 51, 162, 83, 46, 173, 73, 43, 181, 63, 38, 190, 54, 33, 202, 44, 28, 209, 35, 23, 221, 25, 18, 231, 15, 14, 241, 25, 23, 230, 32, 32, 220, 42, 40, 213, 50, 49, 203, 59, 57, 194, 68, 67, 185, 78, 75, 176, 85, 84, 166, 93, 93, 157, 103, 102, 148, 113, 110, 139, 121, 118, 131, 130, 127, 120, 139, 136, 113, 148, 144, 103, 156, 154, 94, 164, 163, 85, 174, 172, 76, 182, 180, 66, 191, 189, 58, 201, 197, 49, 210, 207, 40, 217, 215, 31, 227, 223, 23, 235, 233, 14 };

const byte colorMap_whiteHot[] = { 16, 16, 16, 17, 17, 17, 18, 18, 18, 19, 19, 19, 20, 20, 20, 21, 21, 21, 22, 22, 22, 23, 23, 23, 24, 24, 24, 25, 25, 25, 26, 26, 26, 27, 27, 27, 28, 28, 28, 29, 29, 29, 30, 30, 30, 31, 31, 31, 32, 32, 32, 33, 33, 33, 34, 34, 34, 35, 35, 35, 36, 36, 36, 37, 37, 37, 3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

const byte colorMap_yellow[] = { 62, 16, 15, 63, 17, 16, 61, 18, 15, 62, 19, 16, 61, 20, 16, 61, 22, 15, 59, 22, 15, 60, 23, 16, 60, 23, 16, 60, 25, 15, 60, 25, 15, 61, 26, 16, 59, 27, 16, 58, 28, 14, 59, 29, 15, 59, 31, 14, 59, 31, 14, 60, 32, 15, 61, 34, 15, 59, 34, 15, 60, 36, 14, 60, 37, 15, 60, 37, 15, 61, 39, 14, 61, 39, 14, 60, 40, 15, 61, 42, 14, 61, 42, 14, 62, 43, 15, 63, 44, 15, 63, 46, 16, 64, 47, 15, 64, 47, 15, 65, 49, 14, 65, 50, 15, 66, 52, 14, 66, 52, 14, 68, 52, 15, 68, 54, 15, 68, 54, 15, 69, 55, 14, 70, 56, 15, 71, 57, 16, 72, 57, 14, 72, 59, 15, 73, 60, 14, 75, 61, 13, 76, 62, 14, 78, 64, 15, 78, 64, 15, 79, 65, 14, 80, 66, 15, 82, 67, 14, 83, 68, 15, 84, 69, 14, 84, 69, 14, 85, 71, 14, 88, 71, 15, 89, 72, 14, 90, 73, 15, 93, 75, 15, 94, 76, 14, 95, 78, 13, 98, 78, 14, 99, 79, 14, 100, 80, 15, 102, 81, 14, 103, 82, 15, 105, 82, 14, 106, 84, 13, 107, 85, 14, 110, 85, 14, 110, 85, 14, 113, 87, 14, 114, 88, 15, 117, 89, 14, 119, 91, 14, 120, 92, 14, 122, 93, 15, 123, 94, 14, 125, 95, 13, 126, 96, 14, 129, 96, 13, 130, 97, 14, 132, 98, 13, 133, 99, 13, 136, 100, 14, 138, 100, 13, 139, 101, 14, 141, 102, 13, 144, 105, 14, 147, 106, 14, 148, 107, 13, 150, 107, 14, 153, 108, 13, 154, 109, 14, 156, 110, 13, 157, 111, 12, 158, 112, 13, 160, 113, 13, 161, 114, 14, 164, 114, 13, 166, 115, 12, 167, 116, 13, 170, 116, 12, 172, 119, 13, 174, 119, 12, 176, 121, 14, 178, 122, 13, 179, 123, 14, 182, 124, 13, 183, 125, 13, 185, 125, 14, 185, 126, 12, 186, 127, 13, 189, 127, 12, 190, 128, 13, 192, 129, 12, 194, 131, 12, 195, 132, 13, 196, 134, 13, 199, 135, 13, 202, 136, 14, 203, 137, 13, 203, 137, 13, 205, 138, 12, 206, 139, 12, 207, 140, 13, 208, 141, 12, 209, 142, 13, 209, 142, 13, 212, 143, 12, 213, 144, 13, 215, 146, 13, 215, 147, 12, 217, 149, 12, 219, 149, 13, 220, 151, 12, 221, 152, 13, 221, 152, 11, 222, 153, 12, 223, 154, 13, 224, 155, 12, 224, 155, 12, 225, 157, 12, 226, 158, 13, 227, 159, 12, 228, 160, 13, 228, 160, 11, 229, 161, 12, 230, 163, 11, 231, 164, 12, 231, 166, 12, 231, 166, 12, 232, 167, 13, 233, 168, 12, 233, 168, 12, 234, 169, 13, 232, 170, 11, 233, 171, 12, 233, 171, 12, 234, 174, 12, 234, 174, 12, 235, 175, 11, 233, 176, 11, 235, 179, 12, 235, 179, 12, 235, 180, 13, 235, 181, 11, 236, 182, 12, 235, 182, 12, 236, 183, 13, 234, 184, 11, 235, 185, 12, 235, 187, 11, 235, 187, 11, 233, 188, 11, 234, 189, 12, 233, 190, 11, 234, 191, 12, 234, 193, 13, 234, 193, 11, 232, 194, 11, 232, 196, 12, 232, 196, 12, 231, 197, 13, 231, 198, 11, 231, 199, 12, 231, 199, 12, 231, 201, 11, 229, 202, 11, 230, 203, 12, 229, 204, 12, 229, 204, 11, 228, 206, 12, 227, 207, 12, 227, 208, 13, 225, 209, 11, 226, 210, 12, 225, 211, 12, 223, 212, 12, 223, 212, 12, 223, 214, 11, 223, 216, 12, 223, 216, 12, 221, 217, 10, 222, 218, 11, 221, 218, 11, 220, 220, 12, 220, 220, 12, 219, 223, 11, 219, 223, 11, 217, 224, 11, 217, 225, 12, 217, 226, 11, 215, 226, 11, 215, 228, 12, 216, 229, 11, 215, 230, 11, 215, 230, 11, 214, 232, 12, 213, 233, 12, 213, 233, 10, 212, 235, 11 };
