maxritter/diy-thermocam/firmware/3.0/include/bitmaps.h

/*
*
* BITMAPS - Icons and graphics shown inside the GUI
*
* DIY-Thermocam Firmware
*
* GNU General Public License v3.0
*
* Copyright by Max Ritter
*
* http://www.diy-thermocam.net
* https://github.com/maxritter/diy-thermocam
*
*/

#ifndef BITMAPS_H
#define BITMAPS_H

/*################# PUBLIC CONSTANTS, VARIABLES & DATA TYPES ##################*/

extern const uint16_t iconChangeColorPalette[];
extern const uint8_t iconChangeColorBMP[];
extern const uint16_t iconTempLimitsPalette[];
extern const uint8_t iconTempLimitsBMP[];
extern const uint16_t iconLoadMenuPalette[];
extern const uint8_t iconLoadMenuBMP[];
extern const uint16_t iconShutterPalette[];
extern const uint8_t iconShutterBMP[];
extern const uint16_t iconSettingsMenuPalette[];
extern const uint8_t iconSettingsMenuBMP[];
extern const uint16_t iconDisplaySettingsPalette[];
extern const uint8_t iconDisplaySettingsBMP[];
extern const uint16_t iconDisplayOffPalette[];
extern const uint8_t iconDisplayOffBMP[];
extern const uint16_t iconHotColdPalette[];
extern const uint8_t iconHotColdBMP[];
extern const uint16_t iconTempPointsPalette[];
extern const uint8_t iconTempPointsBMP[];
extern const uint16_t iconBWColors[];
extern const uint8_t iconBWBitmap[];
extern const uint16_t iconReturnColors[];
extern const uint8_t iconReturnBitmap[];
extern const uint16_t iconFWColors[];
extern const uint8_t iconFWBitmap[];
extern const uint16_t logoColors[];
extern const uint8_t logoBitmap[];

#endif /* BITMAPS_H */
