maxritter/diy-thermocam/firmware/3.0/include/colorschemes.h

/*
*
* COLOR SCHEMES - Contains 19 different color schemes to display the thermal image
*
* DIY-Thermocam Firmware
*
* GNU General Public License v3.0
*
* Copyright by Max Ritter
*
* http://www.diy-thermocam.net
* https://github.com/maxritter/diy-thermocam
*
*/

#ifndef COLORSCHEMES_H
#define COLORSCHEMES_H

/*################# PUBLIC CONSTANTS, VARIABLES & DATA TYPES ##################*/

extern const byte colorMap_arctic[];
extern const byte colorMap_blackHot[];
extern const byte colorMap_blueRed[];
extern const byte colorMap_coldest[];
extern const byte colorMap_contrast[];
extern const byte colorMap_doubleRainbow[];
extern const byte colorMap_grayRed[];
extern const byte colorMap_glowBow[];
extern const byte colorMap_grayscale[];
extern const byte colorMap_hottest[];
extern const byte colorMap_ironblack[];
extern const byte colorMap_lava[];
extern const byte colorMap_medical[];
extern const byte colorMap_rainbow[];
extern const byte colorMap_wheel1[];
extern const byte colorMap_wheel2[];
extern const byte colorMap_wheel3[];
extern const byte colorMap_whiteHot[];
extern const byte colorMap_yellow[];

#endif /* COLORSCHEMES_H */
