maxritter/diy-thermocam/firmware/3.0/include/videomenu.h

/*
*
* VIDEO MENU - Record single frames or time interval videos
*
* DIY-Thermocam Firmware
*
* GNU General Public License v3.0
*
* Copyright by Max Ritter
*
* http://www.diy-thermocam.net
* https://github.com/maxritter/diy-thermocam
*
*/

#ifndef VIDEOMENU_H
#define VIDEOMENU_H

/*########################## PUBLIC PROCEDURES ################################*/

void videoCaptureInterval(int16_t* remainingTime, uint32_t* framesCaptured, uint16_t* folderFrames, char* buffer, char* dirName);
void videoCaptureNormal(uint32_t* framesCaptured, uint16_t* folderFrames, char* buffer, char* dirName);
void videoCapture();
bool videoIntervalChooser();
bool videoIntervalHandler(byte* pos);
void videoIntervalString(int pos);
void videoMode();

#endif /* VIDEOMENU_H */
